robotfreak/WatterottRobotStarterKit/Fritzing/Basis-Variante_Steckplatine.png

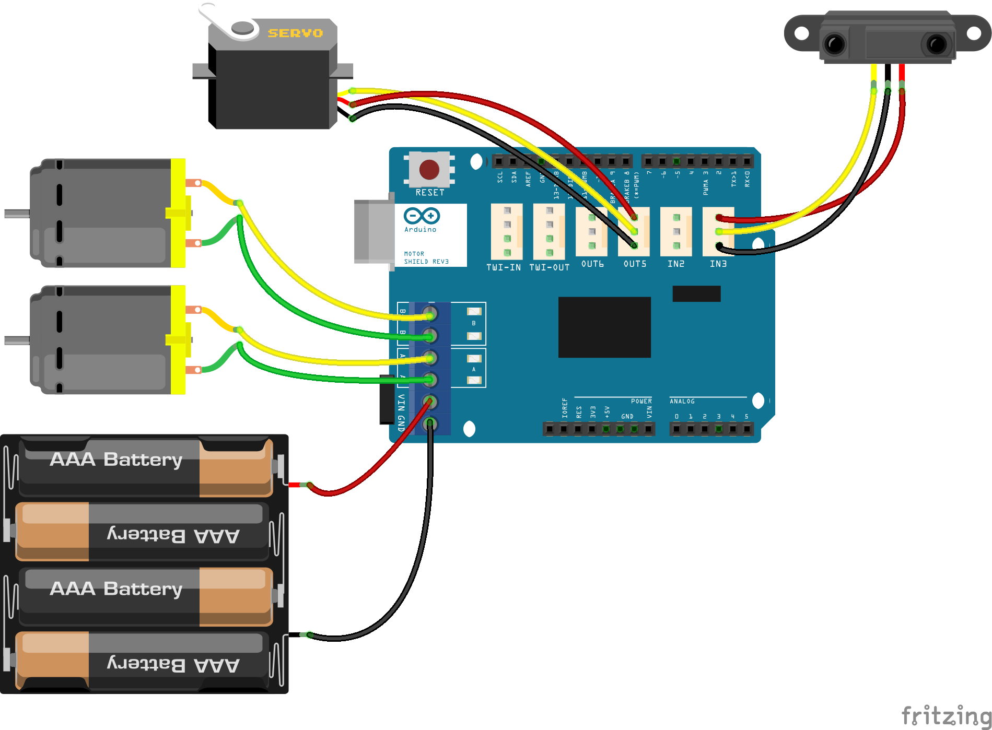
Fritzing/Basis-Variante_Steckplatine.png
